DutchMaker/Apple-1-Mini/docs/PuTTY-setup/PuTTY settings colours.png

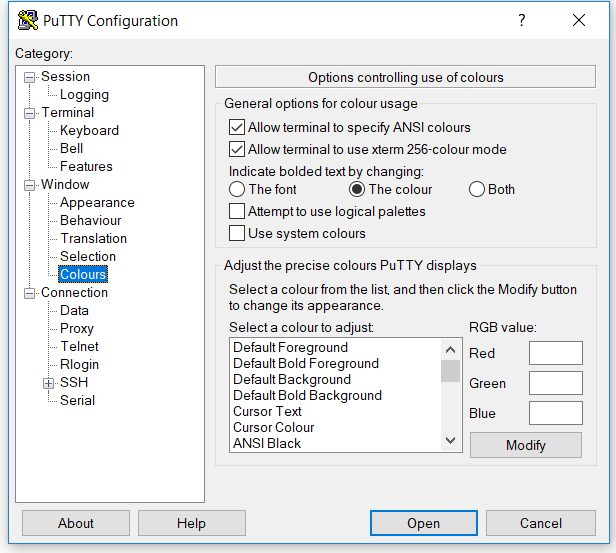
docs/PuTTY-setup/PuTTY settings colours.png
